entozoon/pager-lora/mk-i-pager/hardware/pcb-dev-posterity.png

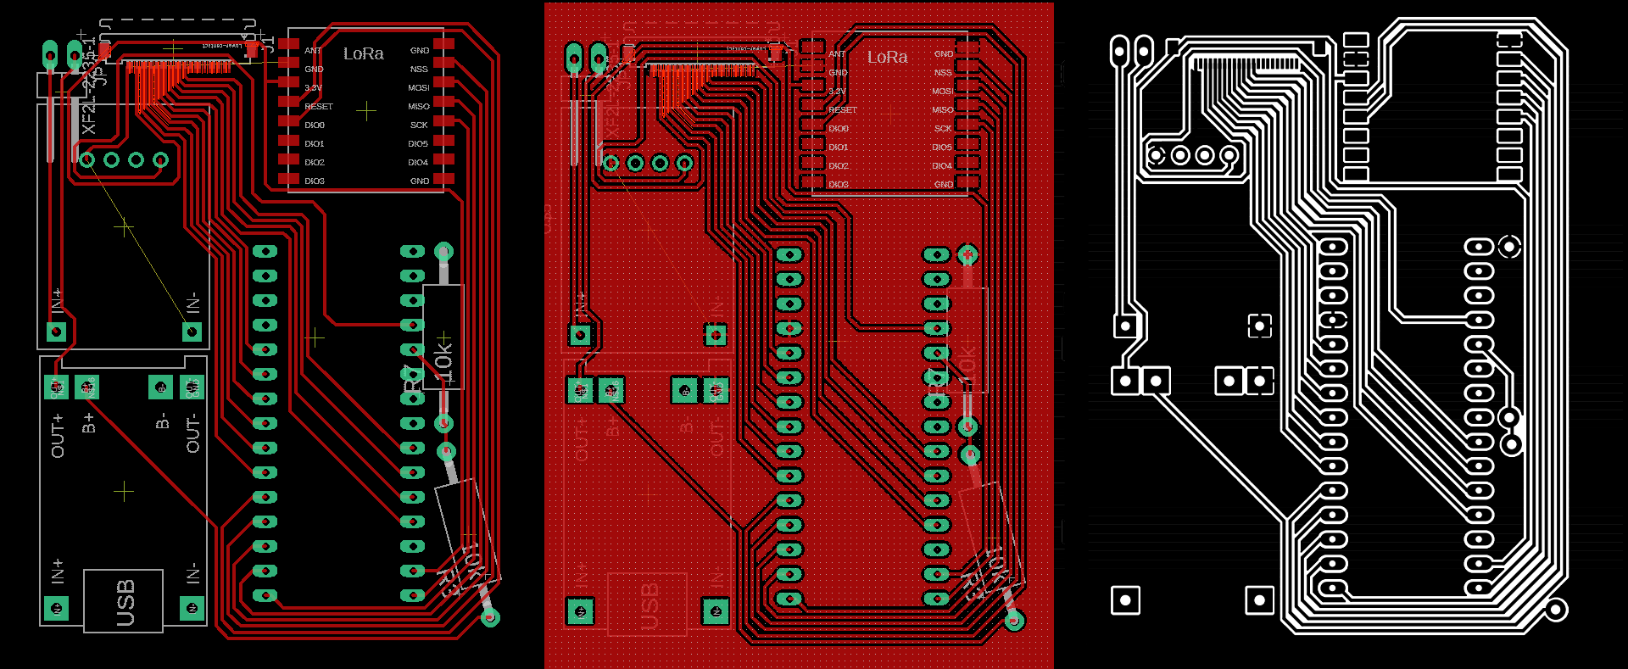
mk-i-pager/hardware/pcb-dev-posterity.png
