entozoon/pager-lora/mk-ii-chokia/hardware/design-2.png

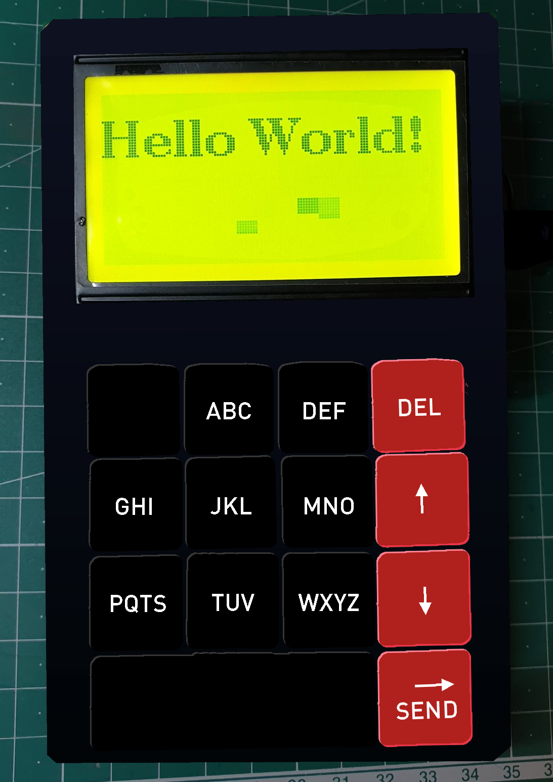
mk-ii-chokia/hardware/design-2.png
