entozoon/pager-lora/mk-ii-chokia/hardware/design-4.png

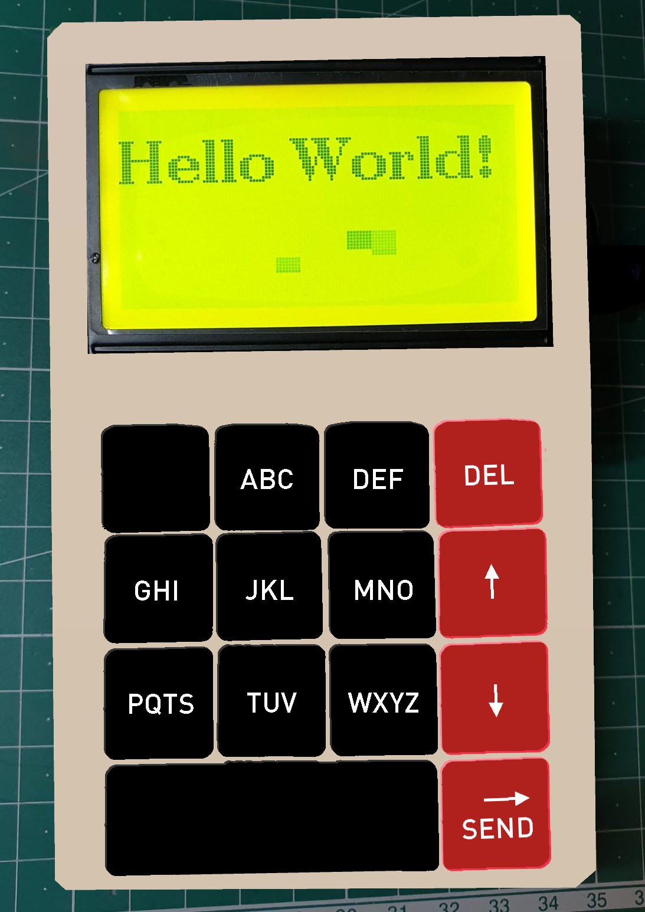
mk-ii-chokia/hardware/design-4.png
