entozoon/pager-lora/mk-i-pager/software/src/nokia-myke.h

const uint8_t __nokiafc224pt7bBitmaps[] PROGMEM = {
    0xFF, 0xCC, 0xB4, 0x57, 0xFE, 0xAF, 0xFD, 0x40, 0x53, 0xF5, 0xE7, 0xAF,
    0xCA, 0xCB, 0x61, 0x0C, 0x21, 0xB4, 0xC0, 0x73, 0x67, 0x3D, 0xDF, 0x77,
    0x40, 0xC0, 0x2B, 0x6D, 0x91, 0x89, 0xB6, 0xD4, 0x25, 0x7E, 0xEF, 0xD4,
    0x80, 0x21, 0x3E, 0x42, 0x00, 0x78, 0xF0, 0xF0, 0x25, 0xAD, 0x20, 0x76,
    0xF7, 0xBD, 0xED, 0xC0, 0x7D, 0xB6, 0xD8, 0xF0, 0xC6, 0xEC, 0x63, 0xE0,
    0xF0, 0xC6, 0xE1, 0x8F, 0xC0, 0x19, 0xD7, 0x3F, 0x8C, 0x60, 0xF4, 0x3C,
    0x31, 0x8F, 0xC0, 0x76, 0x3D, 0xBD, 0xED, 0xC0, 0xF8, 0xCC, 0x66, 0x31,
    0x80, 0x76, 0xF6, 0xED, 0xED, 0xC0, 0x76, 0xF7, 0xB7, 0x8D, 0xC0, 0xF3,
    0xC0, 0xF1, 0xE0, 0x13, 0x6C, 0x63, 0x10, 0xF0, 0xF0, 0x8C, 0x63, 0x6C,
    0x80, 0xF0, 0xCC, 0xC6, 0x01, 0x80, 0x7B, 0x3F, 0xF7, 0xFF, 0x07, 0x80,
    0x76, 0xF7, 0xBF, 0xEF, 0x60, 0xF6, 0xFD, 0xBD, 0xEF, 0xC0, 0x7E, 0x31,
    0x8C, 0x61, 0xE0, 0xF6, 0xF7, 0xBD, 0xEF, 0xC0, 0xFE, 0x3D, 0x8C, 0x63,
    0xE0, 0xFE, 0x3D, 0x8C, 0x63, 0x00, 0x76, 0x31, 0xBD, 0xED, 0xE0, 0xDE,
    0xFF, 0xBD, 0xEF, 0x60, 0xFF, 0xFC, 0x33, 0x33, 0x33, 0xE0, 0xCF, 0x6F,
    0x38, 0xF3, 0x6C, 0xC0, 0xCC, 0xCC, 0xCC, 0xF0, 0x83, 0x8F, 0xBF, 0xFD,
    0x78, 0xF1, 0x80, 0x8F, 0x3E, 0xFF, 0xDF, 0x3C, 0x40, 0x7B, 0x3C, 0xF3,
    0xCF, 0x37, 0x80, 0xF6, 0xF7, 0xBF, 0x63, 0x00, 0x7B, 0x3C, 0xF3, 0xCF,
    0x77, 0x83, 0xF6, 0xF7, 0xBF, 0x6B, 0x60, 0x7C, 0xC6, 0x33, 0xE0, 0xFC,
    0xC3, 0x0C, 0x30, 0xC3, 0x00, 0xDE, 0xF7, 0xBD, 0xED, 0xC0, 0xCF, 0x3C,
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
    {140, 5, 7, 6, 0, -6},  // 0x45 'E'
    {145, 5, 7, 6, 0, -6},  // 0x46 'F'
    {150, 5, 7, 6, 0, -6},  // 0x47 'G'
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

const GFXfont __nokiafc224pt7b PROGMEM = {
    (uint8_t *)__nokiafc224pt7bBitmaps,
    (GFXglyph *)__nokiafc224pt7bGlyphs,
    0x20, 0x7E, 9};

// Approx. 1051 bytes
